dgarcia1985/Arduino-Midi-Wind-Controller/Parts/FreeCAD/Potenciometro.FCStd

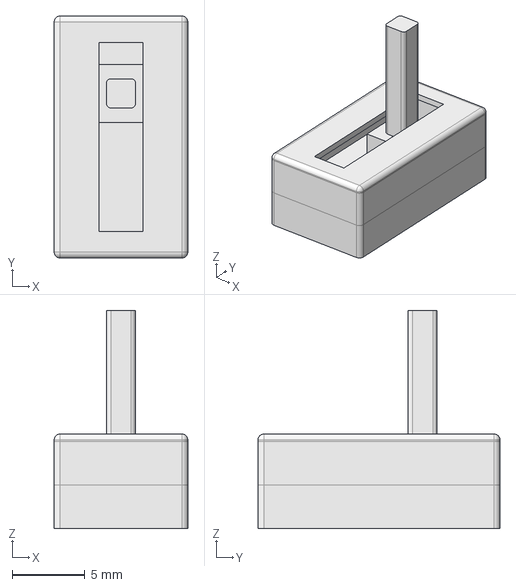
[picture p15: CAD file, 2022-04-15]
Parts/FreeCAD/Potenciometro.FCStd
9.20 x 16.6 x 15.0 mm
