dgarcia1985/Arduino-Midi-Wind-Controller/Parts/FreeCAD/tapas.FCStd

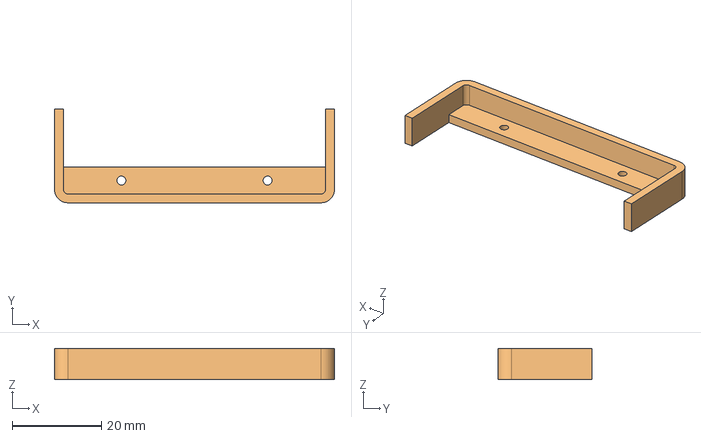
[picture p16: CAD file, 2022-04-15]
Parts/FreeCAD/tapas.FCStd
62.8 x 21.0 x 7.00 mm
