dgarcia1985/Arduino-Midi-Wind-Controller/Parts/FreeCAD/tapa pot linear.FCStd

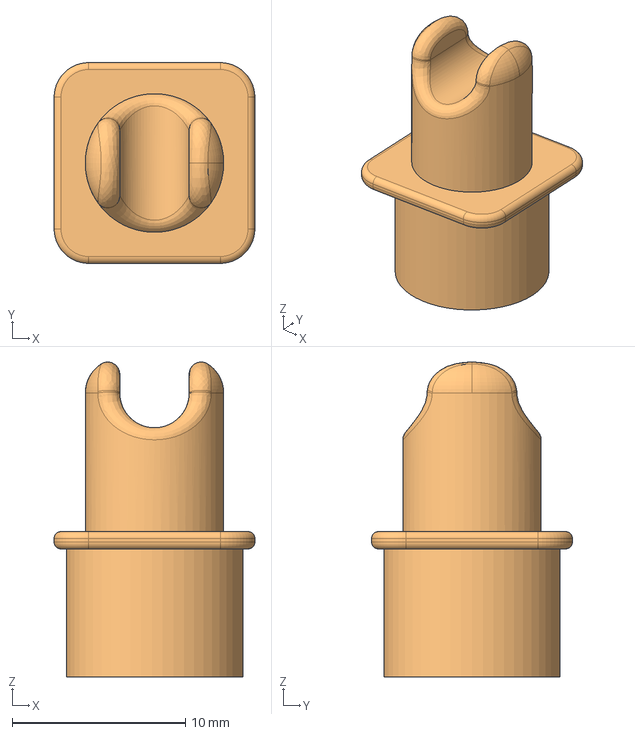
[picture p17: CAD file, 2022-04-15]
Parts/FreeCAD/tapa pot linear.FCStd
11.6 x 11.6 x 18.2 mm
