dgarcia1985/Arduino-Midi-Wind-Controller/Parts/Stl/13 - Boquilla.stl

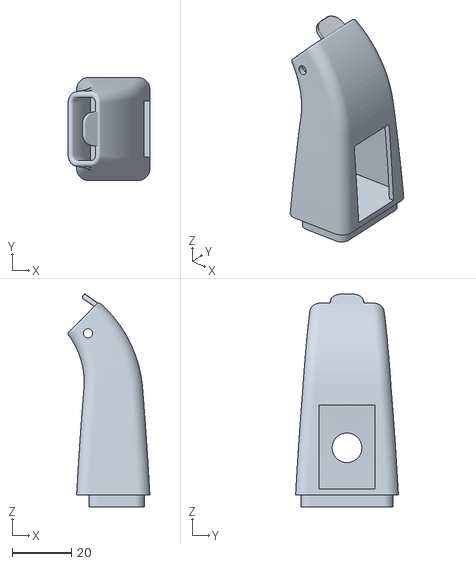
[picture p18: CAD file, 2022-04-15]
Parts/Stl/13 - Boquilla.stl
27.7 x 34.8 x 72.0
