dgarcia1985/Arduino-Midi-Wind-Controller/Parts/FreeCAD/cubierta.FCStd

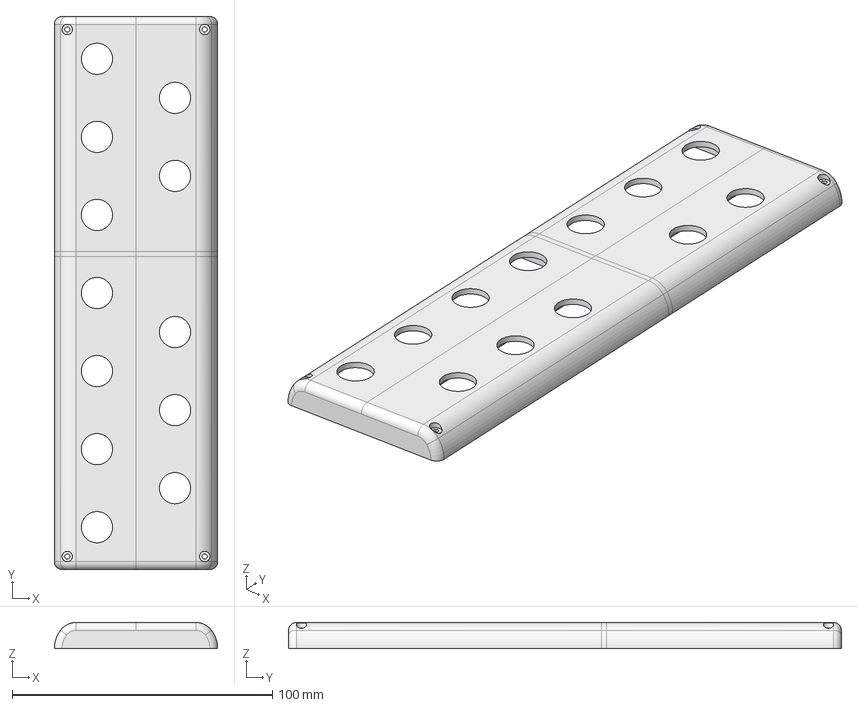
[picture p19: CAD file, 2022-04-15]
Parts/FreeCAD/cubierta.FCStd
62.8 x 212.5 x 10.0 mm
