dgarcia1985/Arduino-Midi-Wind-Controller/Parts/FreeCAD/soporte tornillos arduino 1.FCStd

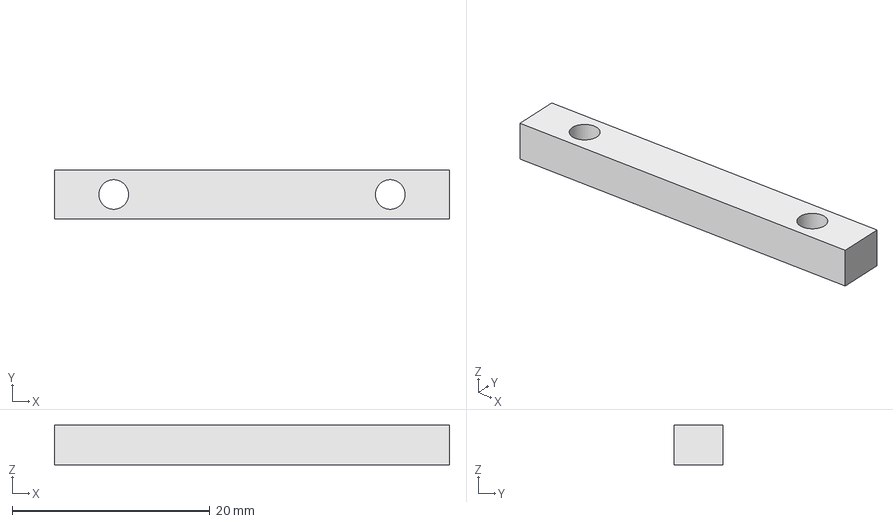
[picture p20: CAD file, 2022-04-15]
Parts/FreeCAD/soporte tornillos arduino 1.FCStd
40.0 x 5.00 x 4.00 mm
