dgarcia1985/Arduino-Midi-Wind-Controller/Parts/Stl/17 - Carcasa Potenciometro.stl

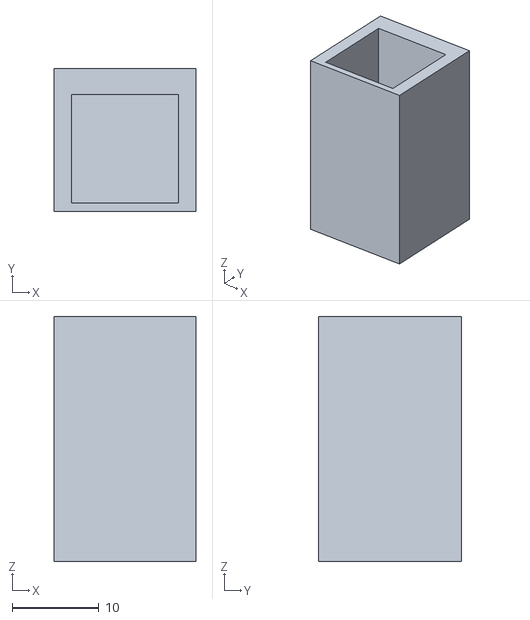
[picture p21: CAD file, 2022-04-15]
Parts/Stl/17 - Carcasa Potenciometro.stl
16.4 x 16.5 x 28.3
