dgarcia1985/Arduino-Midi-Wind-Controller/Parts/FreeCAD/Eje Joystick.FCStd

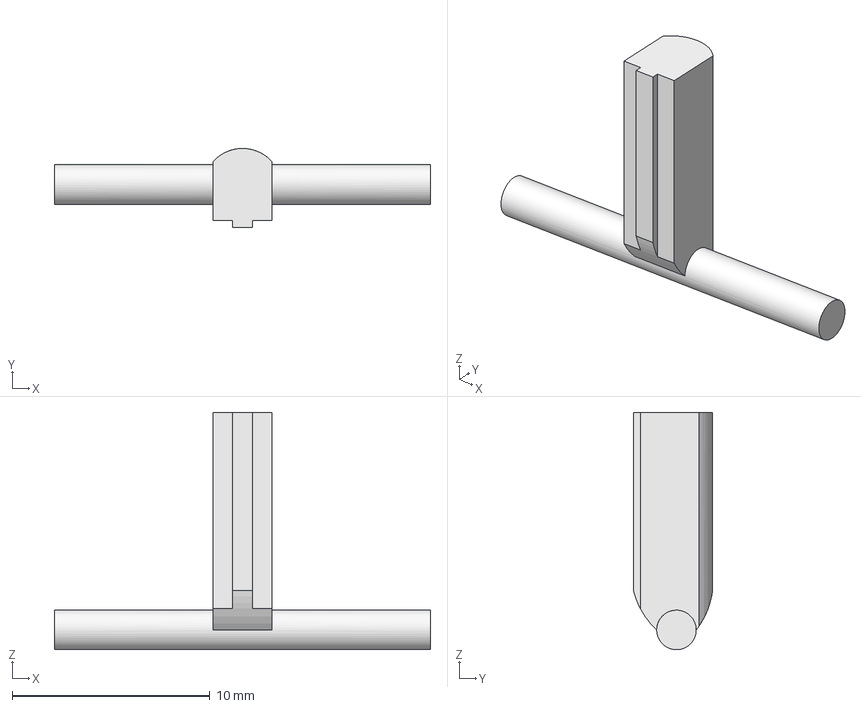
[picture p22: CAD file, 2022-04-15]
Parts/FreeCAD/Eje Joystick.FCStd
19.0 x 4.00 x 12.0 mm
