dgarcia1985/Arduino-Midi-Wind-Controller/Parts/FreeCAD/carcasa arduino.FCStd

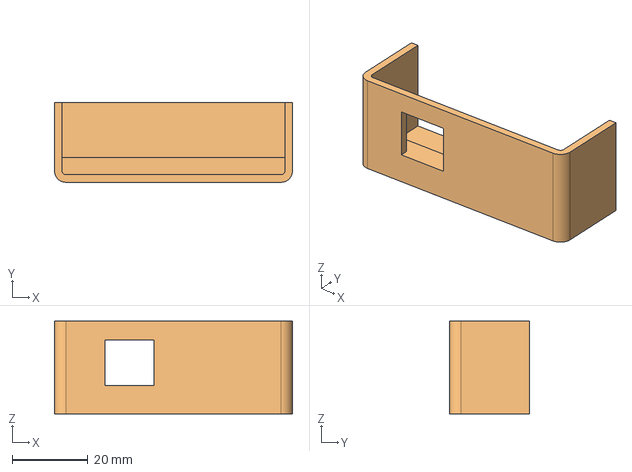
[picture p23: CAD file, 2022-04-15]
Parts/FreeCAD/carcasa arduino.FCStd
62.8 x 21.0 x 24.5 mm
