dgarcia1985/Arduino-Midi-Wind-Controller/Parts/FreeCAD/Pulsador Boton.FCStd

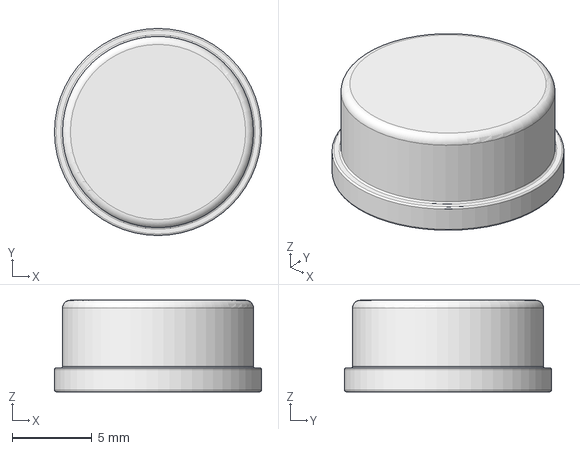
[picture p24: CAD file, 2022-04-15]
Parts/FreeCAD/Pulsador Boton.FCStd
13.0 x 13.0 x 5.75 mm
