dgarcia1985/Arduino-Midi-Wind-Controller/Parts/FreeCAD/eje.FCStd

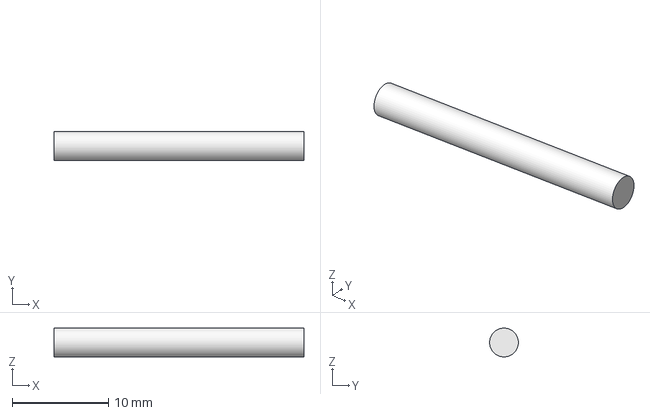
[picture p25: CAD file, 2022-04-15]
Parts/FreeCAD/eje.FCStd
26.0 x 3.00 x 3.00 mm
