dgarcia1985/Arduino-Midi-Wind-Controller/Parts/FreeCAD/carcasa pot linear.FCStd

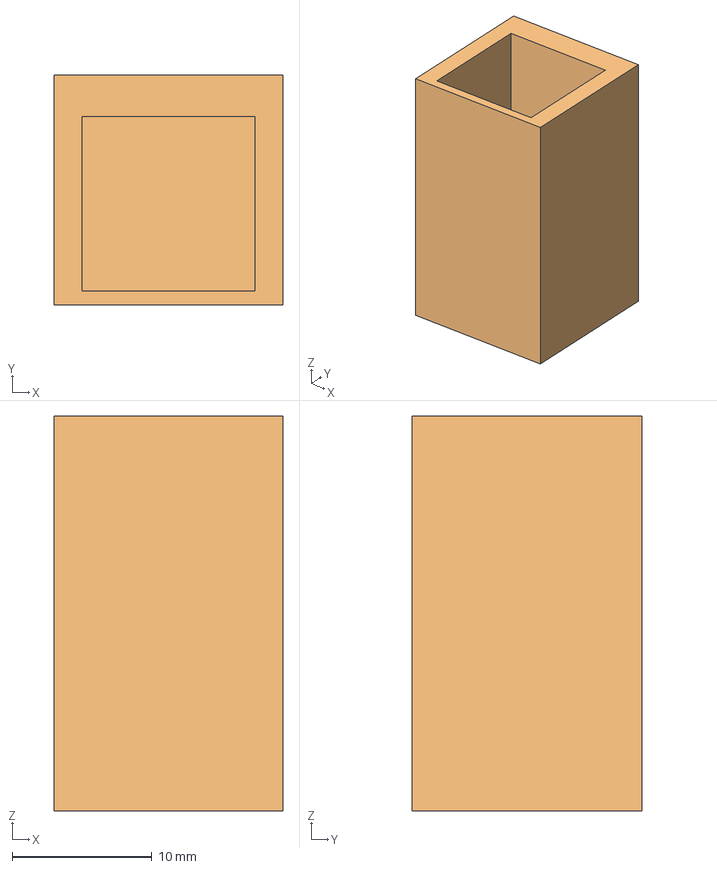
[picture p26: CAD file, 2022-04-15]
Parts/FreeCAD/carcasa pot linear.FCStd
16.4 x 16.5 x 28.3 mm
