dgarcia1985/Arduino-Midi-Wind-Controller/Parts/FreeCAD/Base boton.FCStd

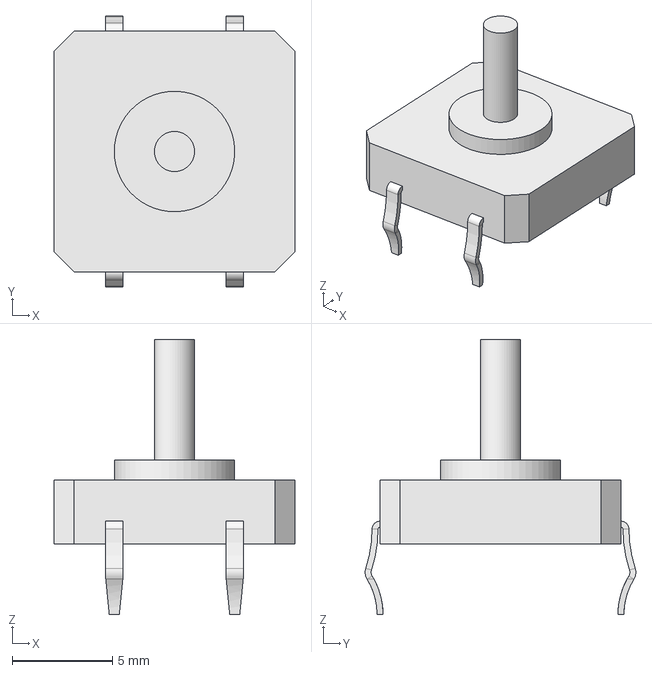
[picture p27: CAD file, 2022-04-15]
Parts/FreeCAD/Base boton.FCStd
12.0 x 13.5 x 13.7 mm
