dgarcia1985/Arduino-Midi-Wind-Controller/Parts/FreeCAD/placa resistencias.FCStd

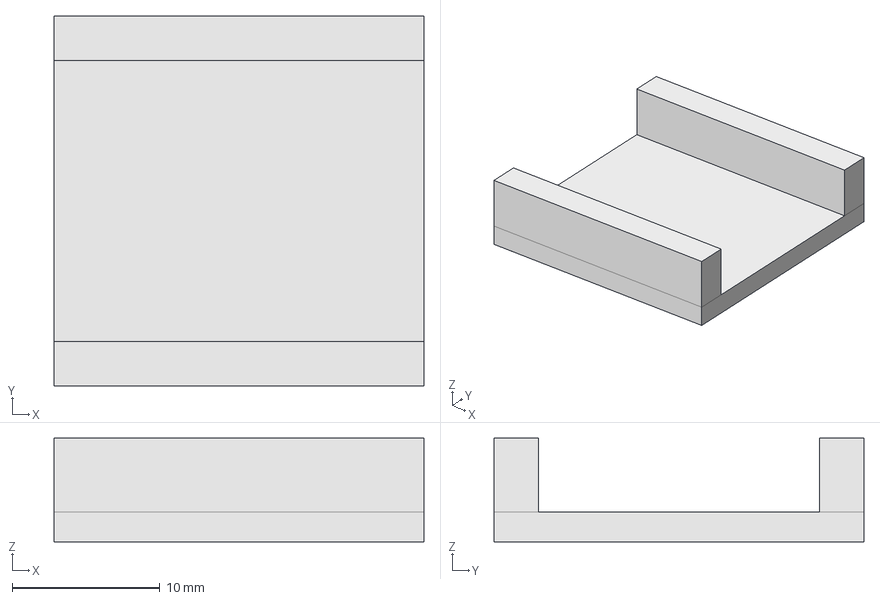
[picture p28: CAD file, 2022-04-15]
Parts/FreeCAD/placa resistencias.FCStd
25.0 x 25.0 x 7.00 mm
