dgarcia1985/Arduino-Midi-Wind-Controller/Parts/FreeCAD/enganche boquilla.FCStd

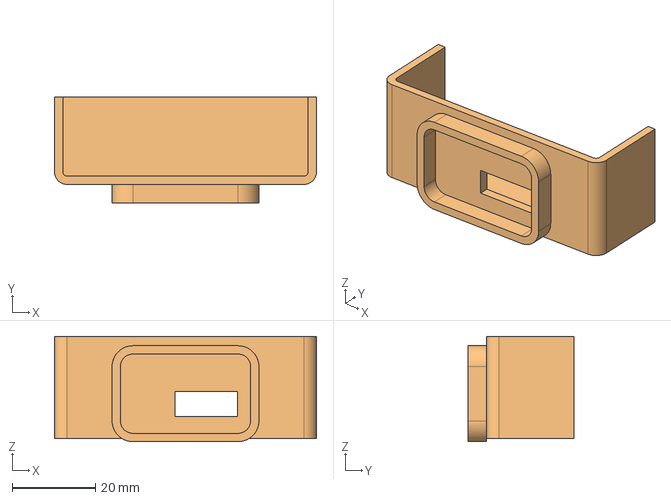
[picture p29: CAD file, 2022-04-15]
Parts/FreeCAD/enganche boquilla.FCStd
62.8 x 25.5 x 25.3 mm
