dgarcia1985/Arduino-Midi-Wind-Controller/Parts/FreeCAD/Arduino Uno.FCStd

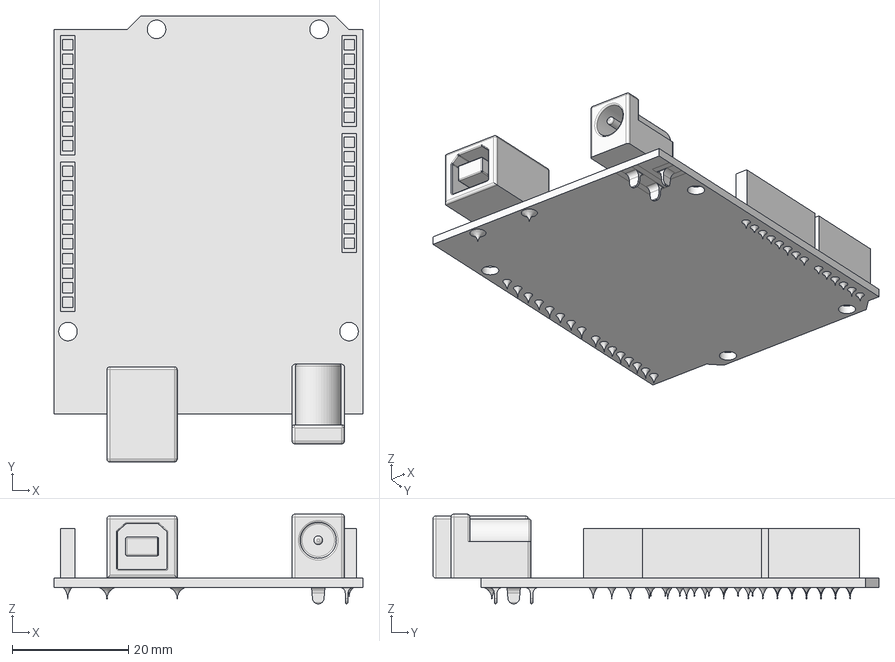
[picture p30: CAD file, 2022-04-15]
Parts/FreeCAD/Arduino Uno.FCStd
53.2 x 76.8 x 15.4 mm
