dgarcia1985/Arduino-Midi-Wind-Controller/Parts/FreeCAD/Muelle.FCStd

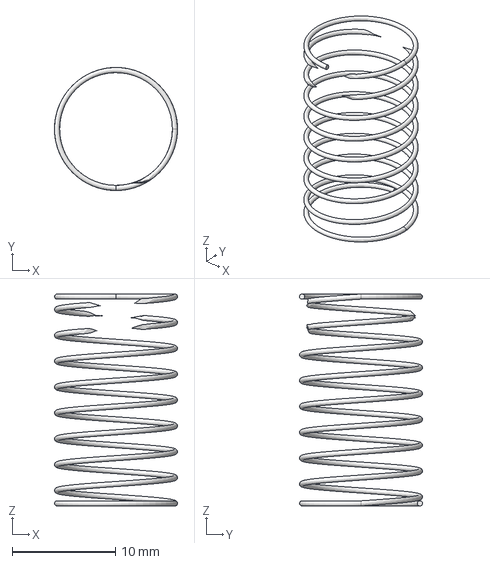
[picture p31: CAD file, 2022-04-15]
Parts/FreeCAD/Muelle.FCStd
11.9 x 11.9 x 20.5 mm
